impatrq/ecosorter/Códigos/Sistema de puntos/assets/images/fondo.png

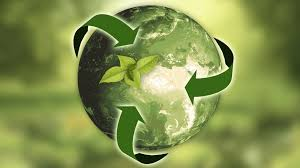
Códigos/Sistema de puntos/assets/images/fondo.png
