impatrq/ecosorter/impresiones 3D/foto cv.jpg

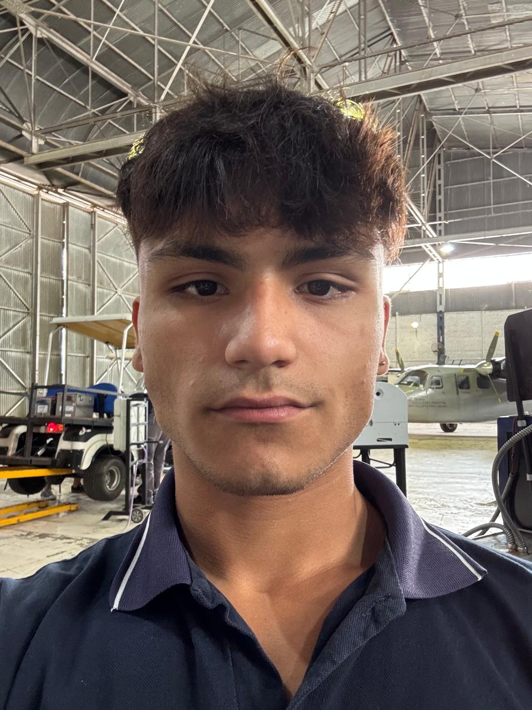
impresiones 3D/foto cv.jpg
