impatrq/ecosorter/Página web/images/descarga__7_-removebg-preview.png

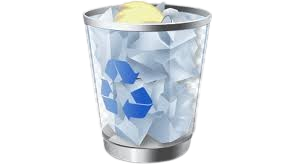
Página web/images/descarga__7_-removebg-preview.png
