impatrq/ecosorter/Página web/images/imagen_2024-07-30_093741966.png

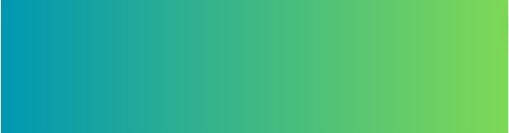
Página web/images/imagen_2024-07-30_093741966.png
