impatrq/ecosorter/Página web/images/imagen_2024-08-01_093056349-removebg-preview.png

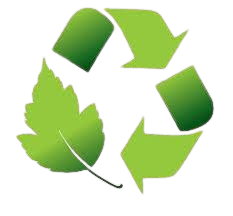
Página web/images/imagen_2024-08-01_093056349-removebg-preview.png
