impatrq/ecosorter/Página web/images/imagen_2024-08-02_082747121-removebg-preview.png

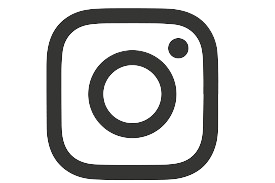
Página web/images/imagen_2024-08-02_082747121-removebg-preview.png
