impatrq/ecosorter/Página web/images/imagen_2024-08-02_082923932-removebg-preview.png

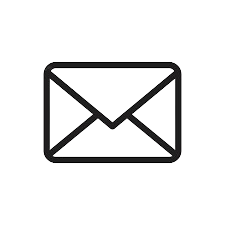
Página web/images/imagen_2024-08-02_082923932-removebg-preview.png
