impatrq/ecosorter/Página web/images/imagen_2024-08-07_105342505.png

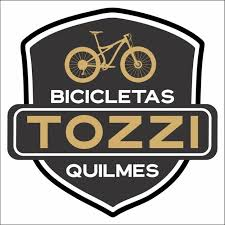
Página web/images/imagen_2024-08-07_105342505.png
