impatrq/ecosorter/Página web/images/imagen_2024-08-23_110759560.png

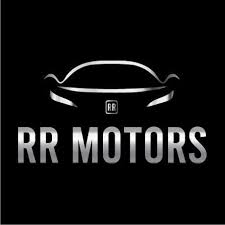
Página web/images/imagen_2024-08-23_110759560.png
