impatrq/ecosorter/Página web/images/imagen_2024-08-27_110544253-p-500.png

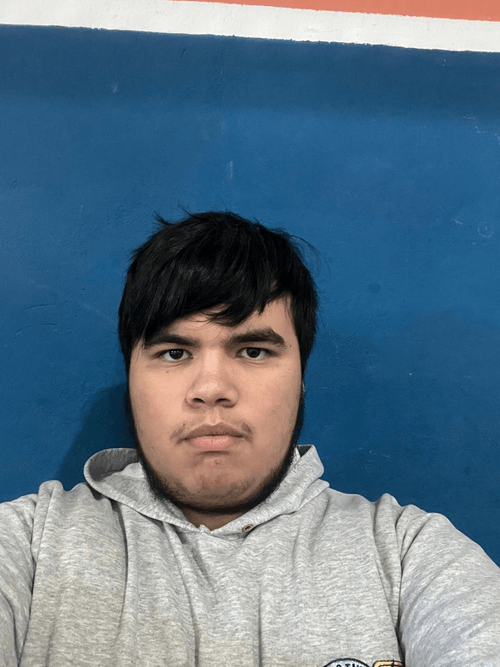
Página web/images/imagen_2024-08-27_110544253-p-500.png
