impatrq/ecosorter/Página web/images/imagen_2024-08-28_082841518-p-500.png

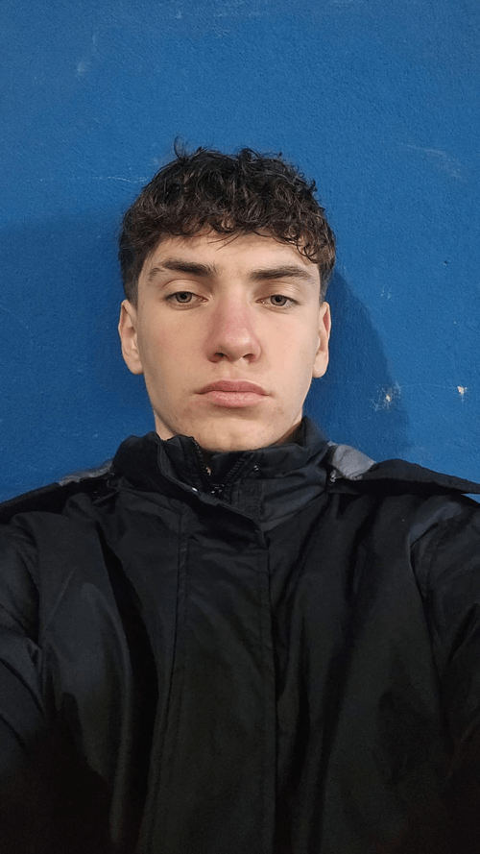
Página web/images/imagen_2024-08-28_082841518-p-500.png
