impatrq/ecosorter/Página web/images/imagen_2024-09-09_143702266-p-500.png

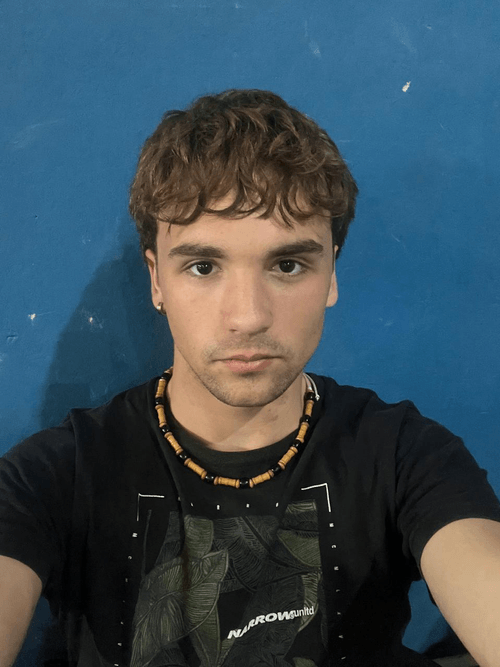
Página web/images/imagen_2024-09-09_143702266-p-500.png
