impatrq/ecosorter/Página web/images/imagen_2024-09-09_143903477.png

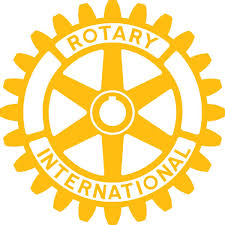
Página web/images/imagen_2024-09-09_143903477.png
