impatrq/ecosorter/Página web/images/imagen_2024-11-14_105533027-removebg-preview.png

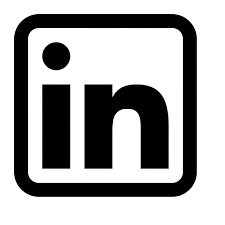
Página web/images/imagen_2024-11-14_105533027-removebg-preview.png
