impatrq/ecosorter/Página web/images/img_9907-min-p-500.jpg

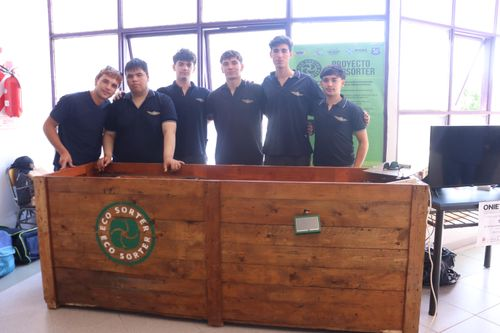
Página web/images/img_9907-min-p-500.jpg
