impatrq/ecosorter/Documentación/manual de intrucciones de armado eco sorterr.png

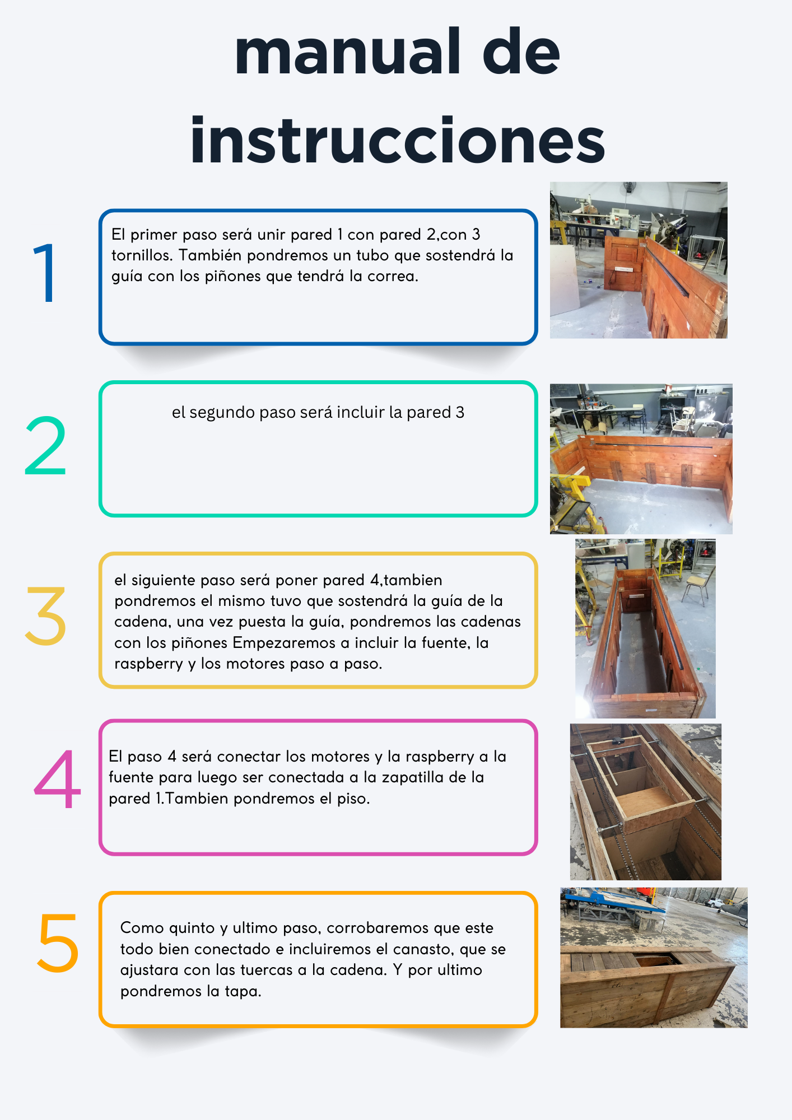
Documentación/manual de intrucciones de armado eco sorterr.png
